Joshua-Benfell/ECEN405_ClassDAmplifier/figures/1.1_Waves (3).png

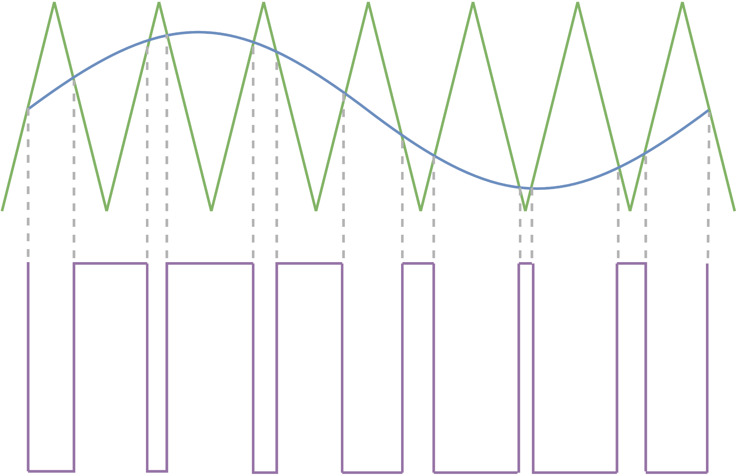
figures/1.1_Waves (3).png
