Joshua-Benfell/ECEN405_ClassDAmplifier/figures/5vSupply.png

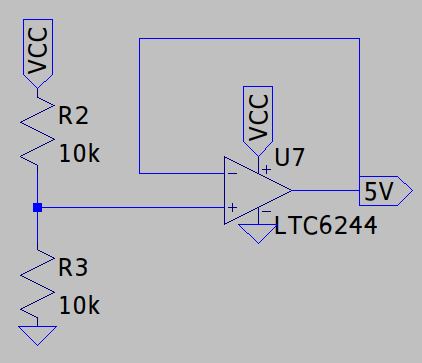
figures/5vSupply.png
