Joshua-Benfell/ECEN405_ClassDAmplifier/figures/angle2.jpg

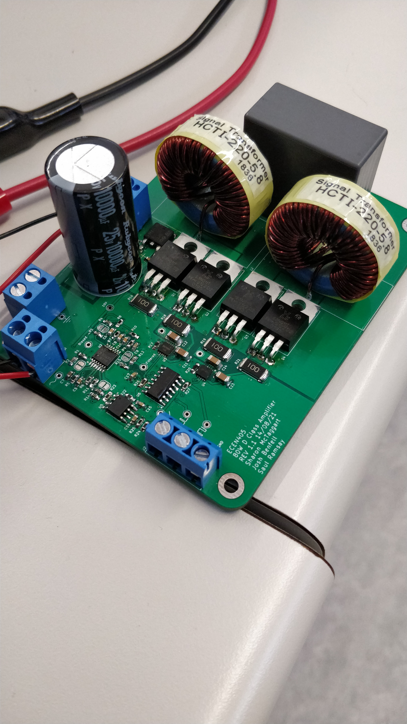
figures/angle2.jpg
