Joshua-Benfell/ECEN405_ClassDAmplifier/figures/backPCB.png

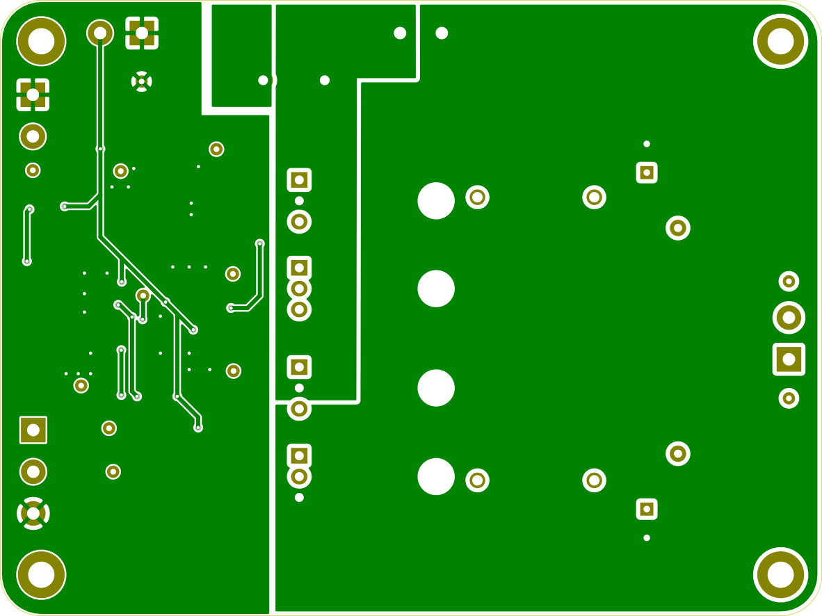
figures/backPCB.png
