Joshua-Benfell/ECEN405_ClassDAmplifier/figures/BiasedSignal.JPG

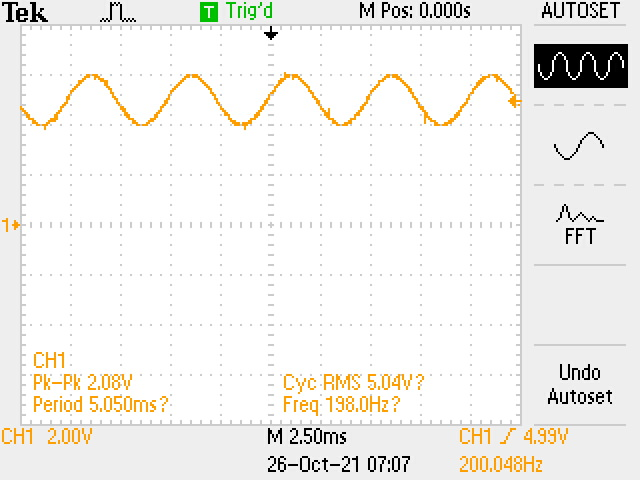
figures/BiasedSignal.JPG
