Joshua-Benfell/ECEN405_ClassDAmplifier/figures/biasingHPF.png

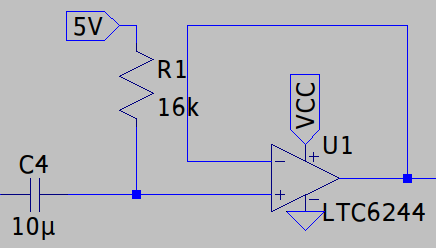
figures/biasingHPF.png
