Joshua-Benfell/ECEN405_ClassDAmplifier/figures/bodeChart.png

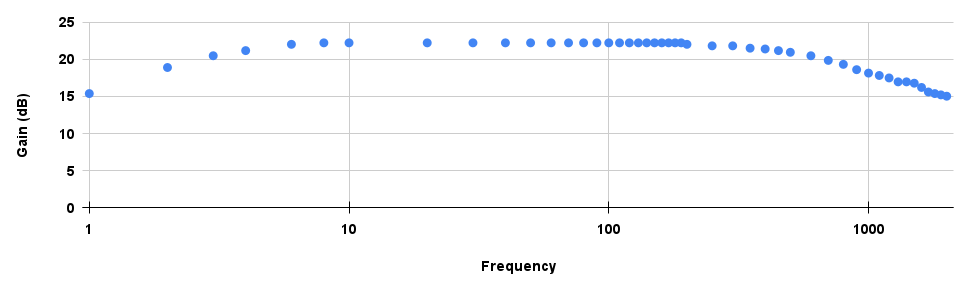
figures/bodeChart.png
