Joshua-Benfell/ECEN405_ClassDAmplifier/figures/bothPWM.JPG

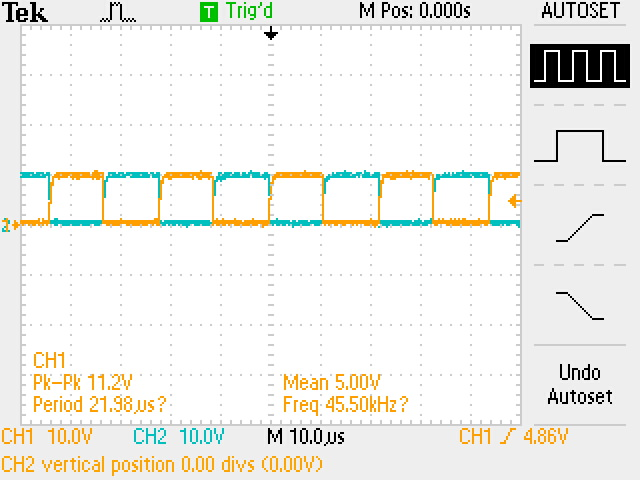
figures/bothPWM.JPG
