Joshua-Benfell/ECEN405_ClassDAmplifier/figures/bpfBode.png

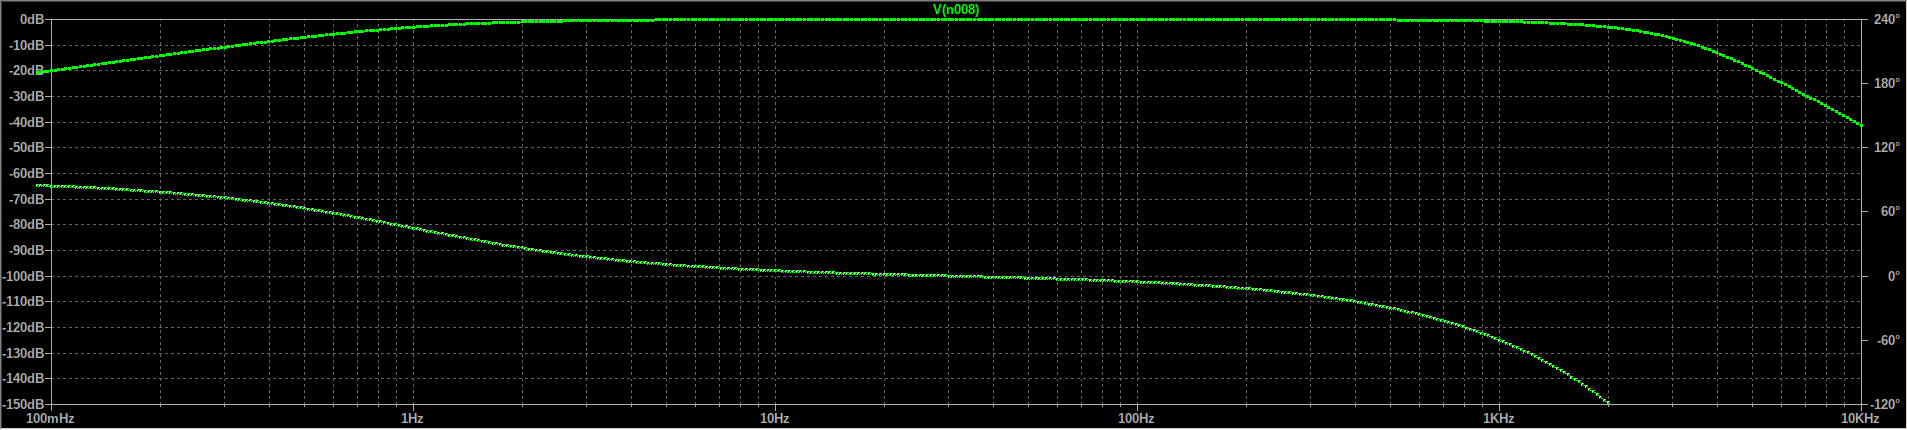
figures/bpfBode.png
