Joshua-Benfell/ECEN405_ClassDAmplifier/figures/Deadtime.png

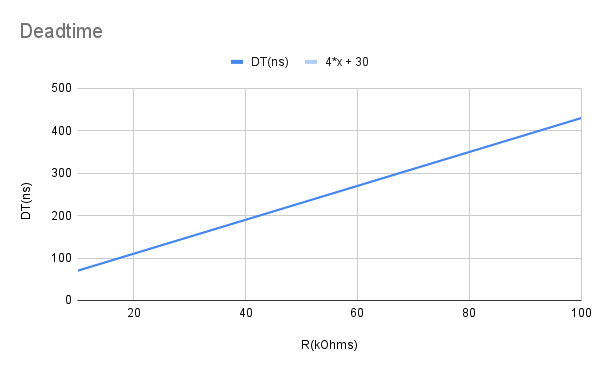
figures/Deadtime.png
