Joshua-Benfell/ECEN405_ClassDAmplifier/figures/efficiencyChart.png

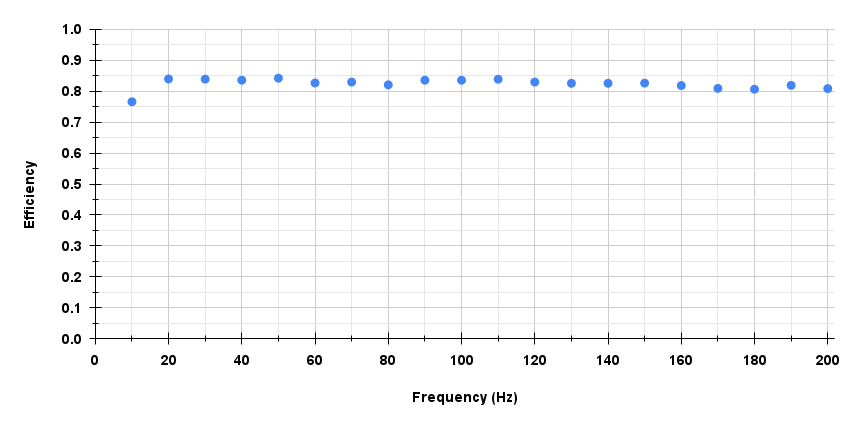
figures/efficiencyChart.png
