Joshua-Benfell/ECEN405_ClassDAmplifier/figures/frontPCB.png

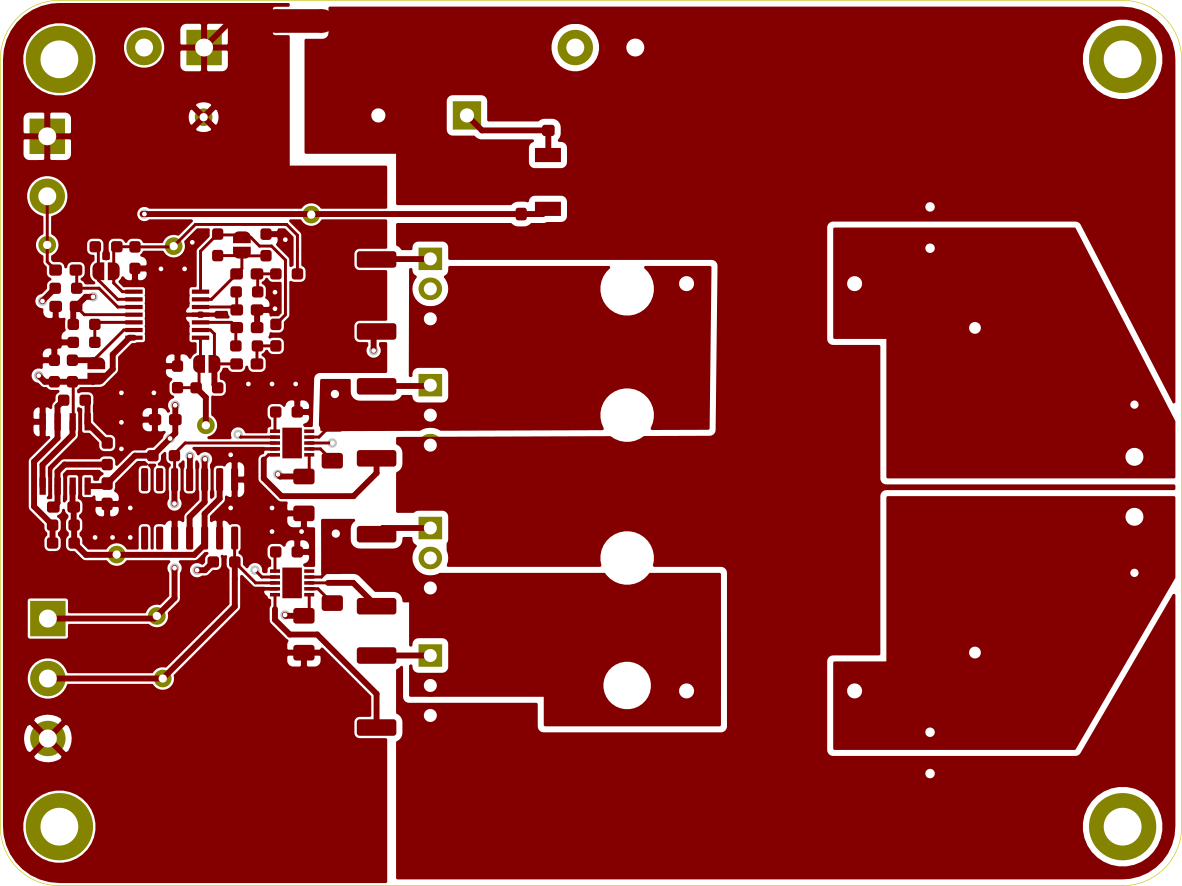
figures/frontPCB.png
