Joshua-Benfell/ECEN405_ClassDAmplifier/figures/fullbridge.jpg

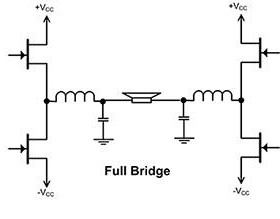
figures/fullbridge.jpg
