Joshua-Benfell/ECEN405_ClassDAmplifier/figures/highDCPWM.JPG

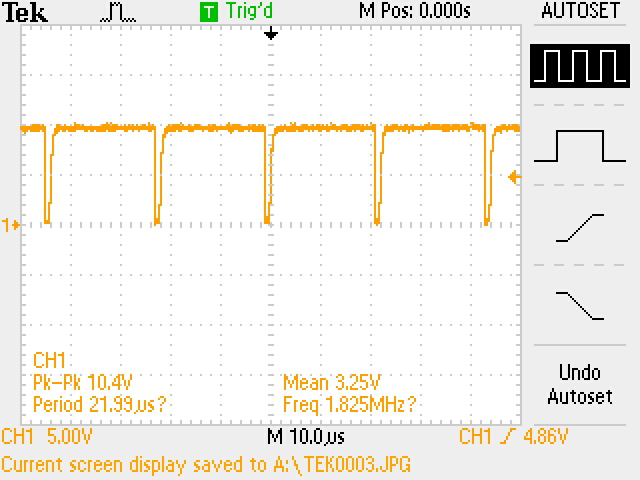
figures/highDCPWM.JPG
