Joshua-Benfell/ECEN405_ClassDAmplifier/figures/hpfBode.png

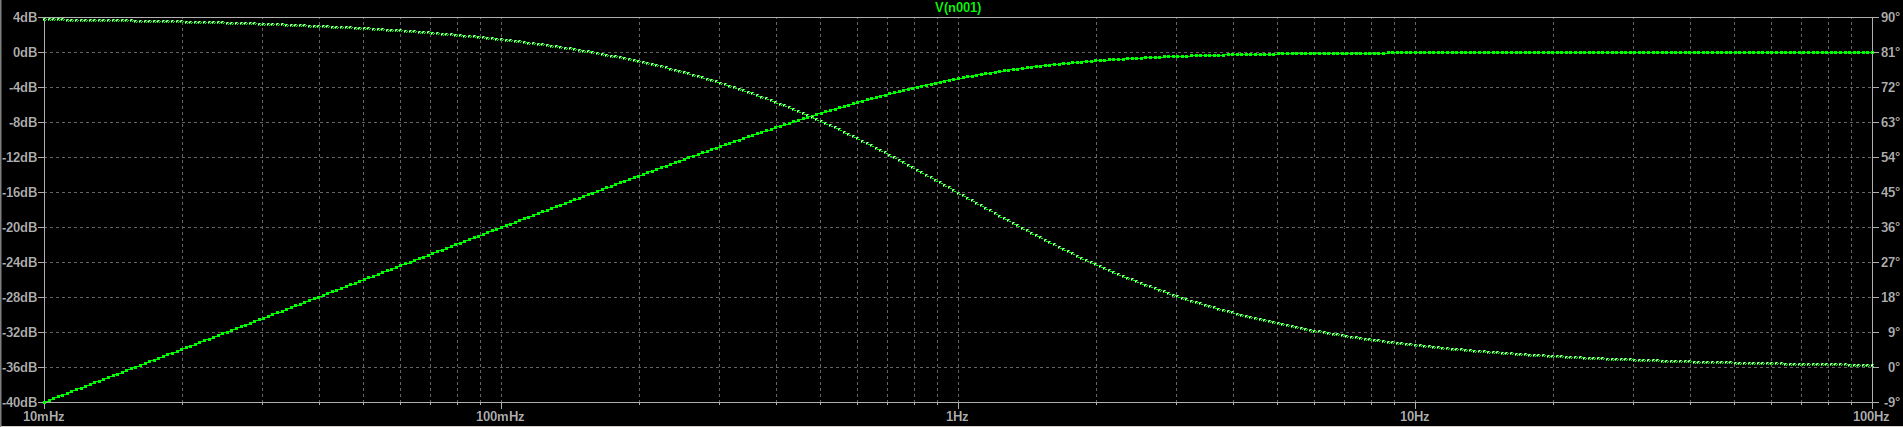
figures/hpfBode.png
