Joshua-Benfell/ECEN405_ClassDAmplifier/figures/outputFilterBode.png

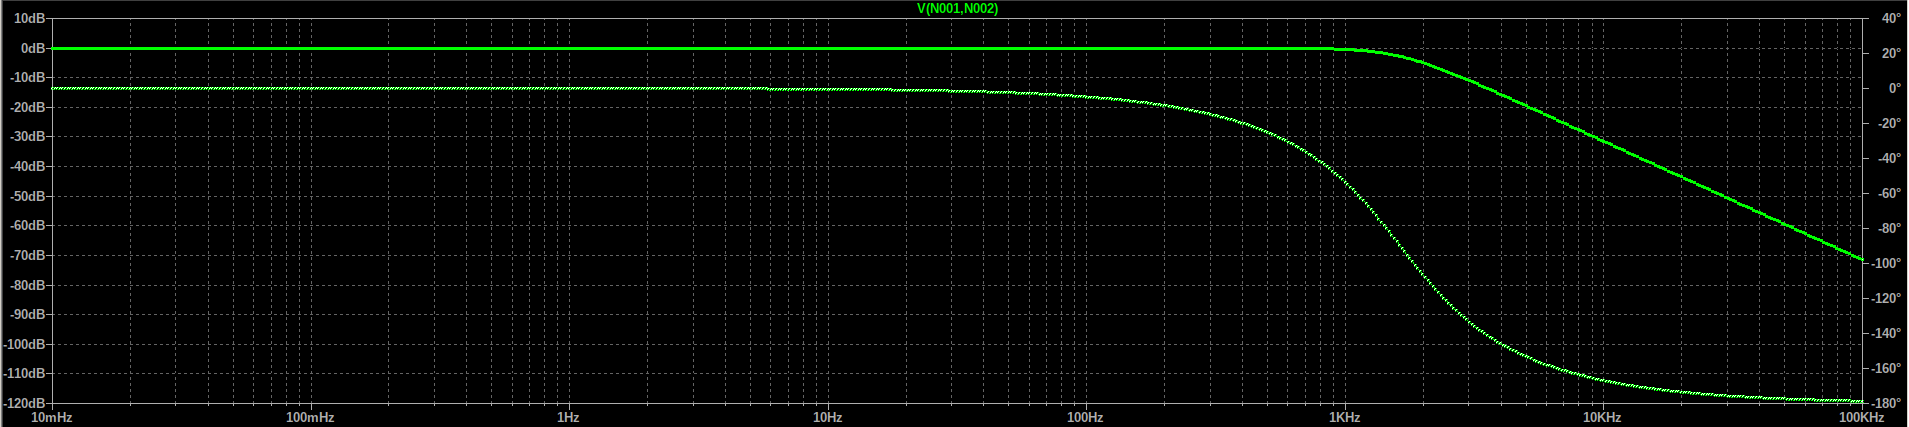
figures/outputFilterBode.png
