Joshua-Benfell/ECEN405_ClassDAmplifier/figures/outputSignalLoadedBySpeaker.JPG

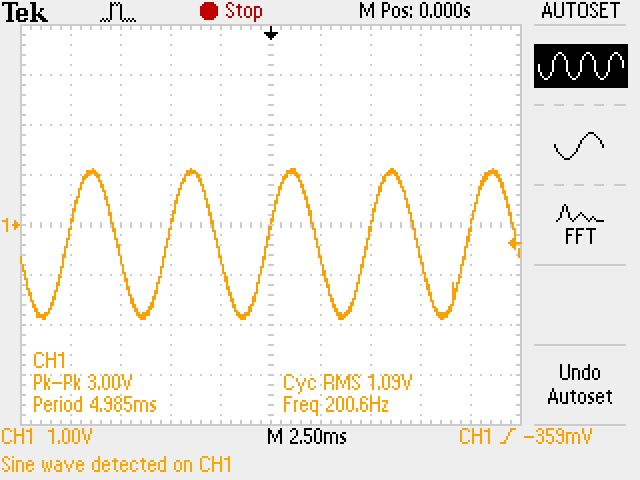
figures/outputSignalLoadedBySpeaker.JPG
