Joshua-Benfell/ECEN405_ClassDAmplifier/figures/systemBlockDiagram.png

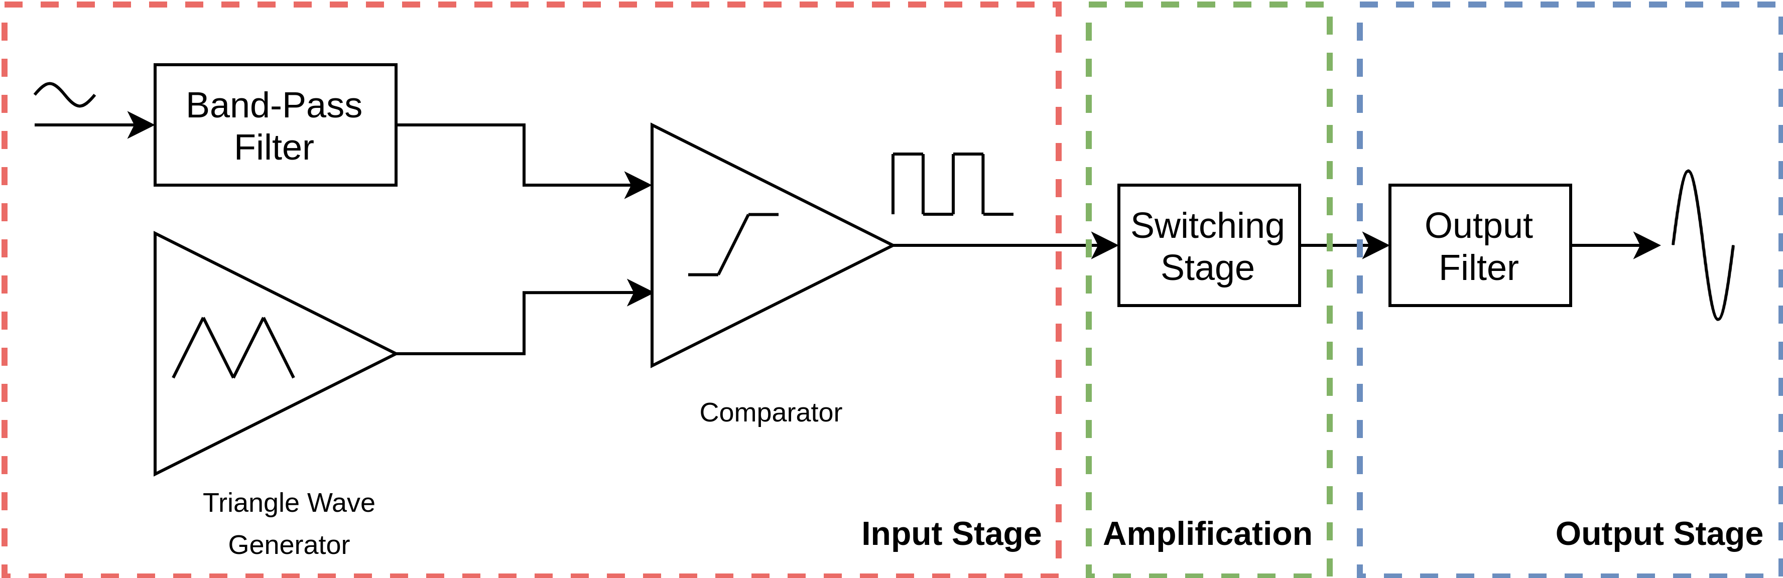
figures/systemBlockDiagram.png
