Joshua-Benfell/ECEN405_ClassDAmplifier/figures/THD.jpg

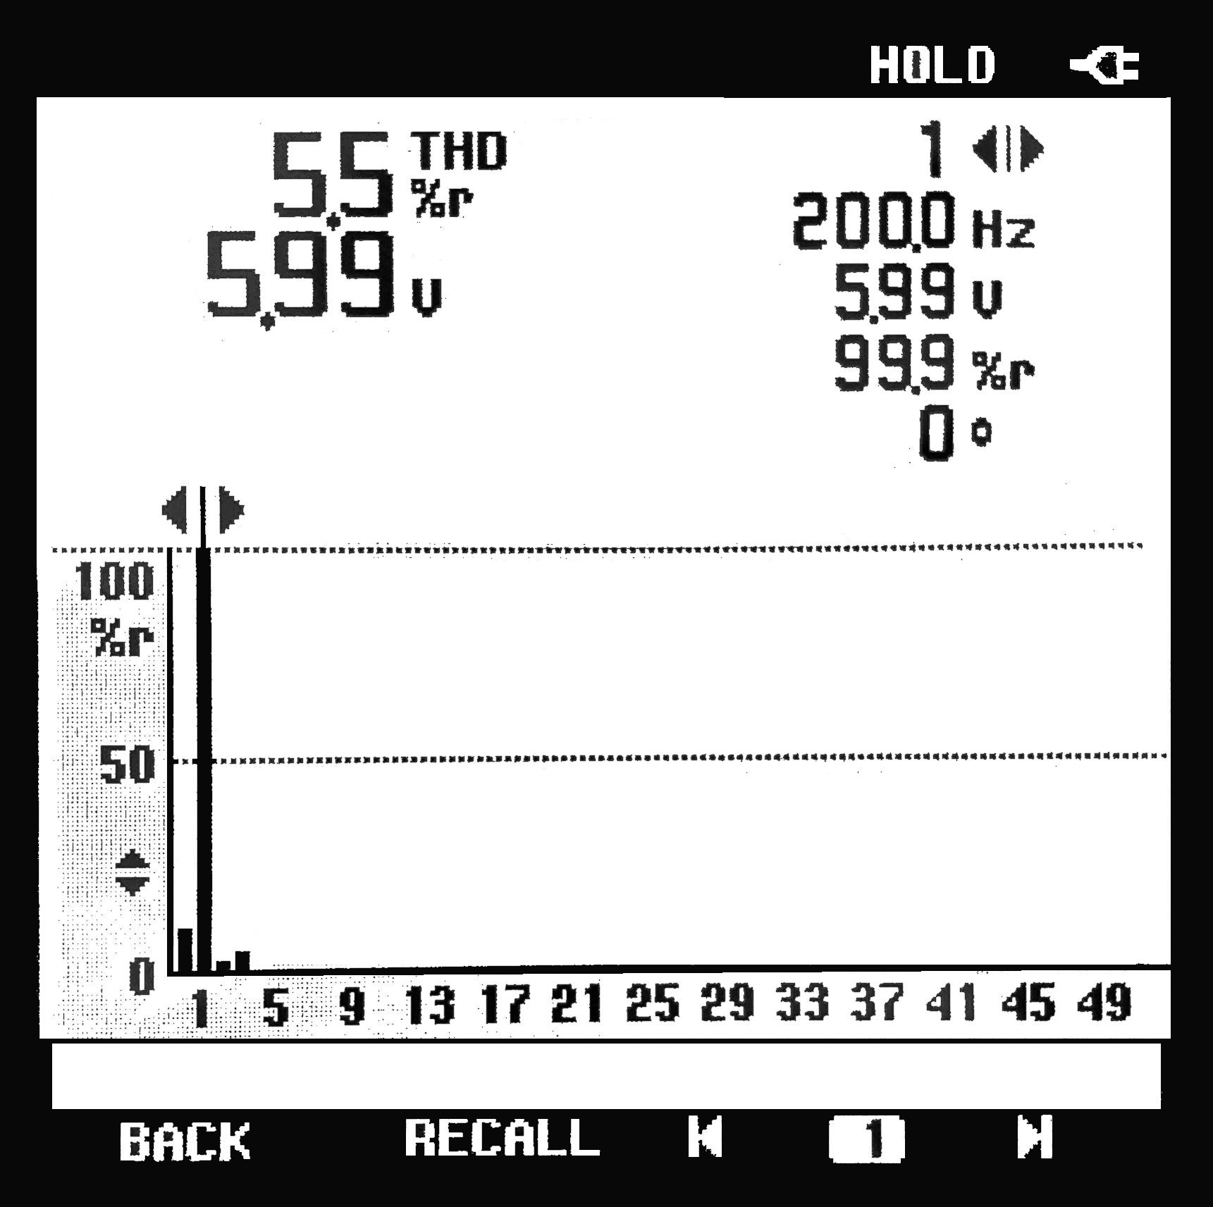
figures/THD.jpg
