Joshua-Benfell/ECEN405_ClassDAmplifier/figures/THDChart.png

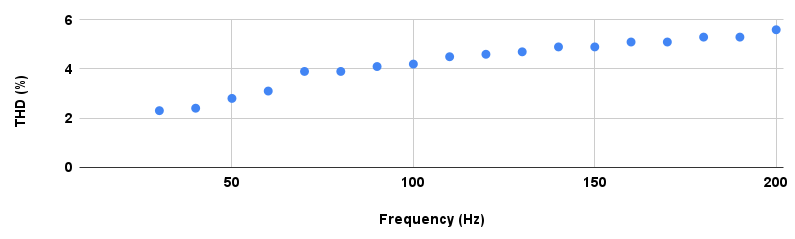
figures/THDChart.png
