Joshua-Benfell/ECEN405_ClassDAmplifier/figures/topdown.jpg

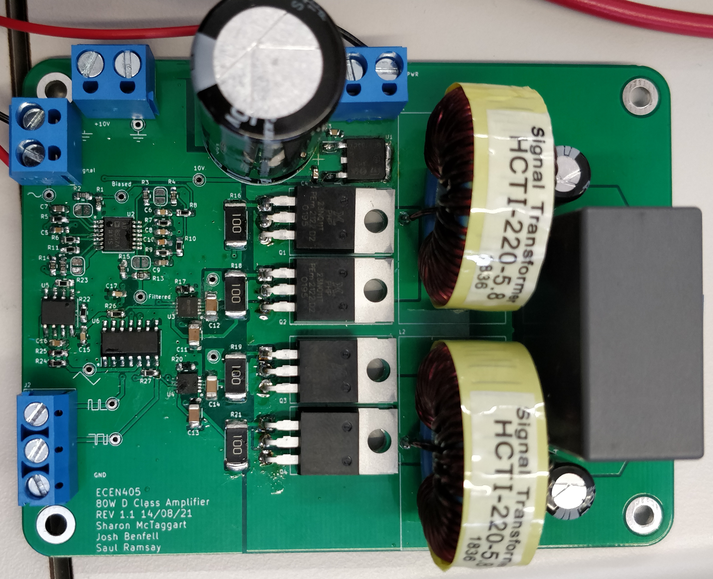
figures/topdown.jpg
