Joshua-Benfell/ECEN405_ClassDAmplifier/figures/triangleOverlappingSignal.JPG

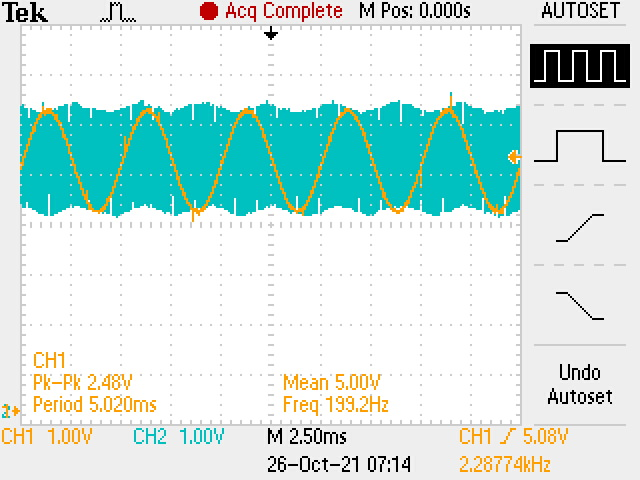
figures/triangleOverlappingSignal.JPG
