Joshua-Benfell/ECEN405_ClassDAmplifier/figures/TriangleWave.JPG

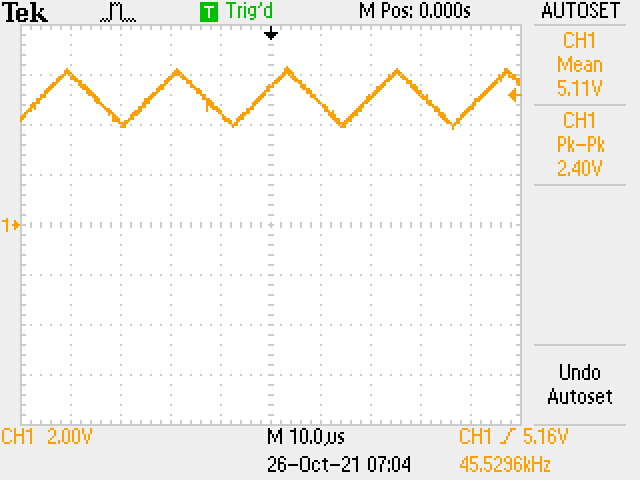
figures/TriangleWave.JPG
