Joshua-Benfell/ECEN405_ClassDAmplifier/figures/triangleWave.png

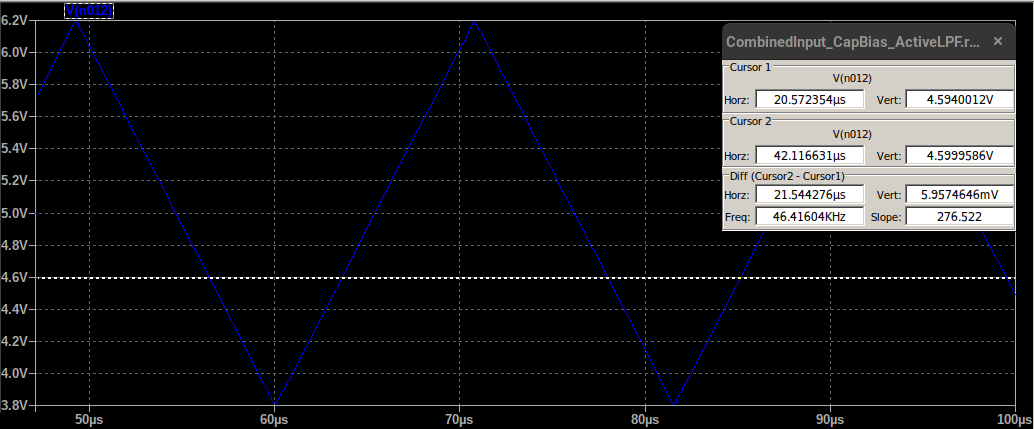
figures/triangleWave.png
