Joshua-Benfell/ECEN405_ClassDAmplifier/figures/triangleWaveGenerator.png

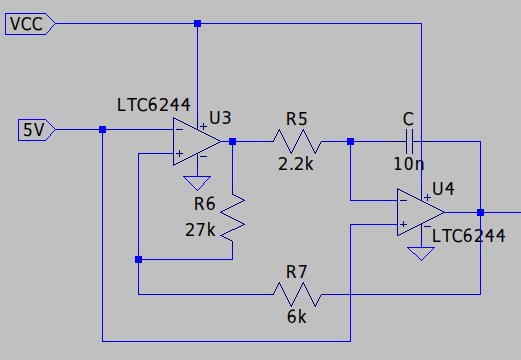
figures/triangleWaveGenerator.png
