Joshua-Benfell/ECEN405_ClassDAmplifier/Kicad/Output/Output1A.png

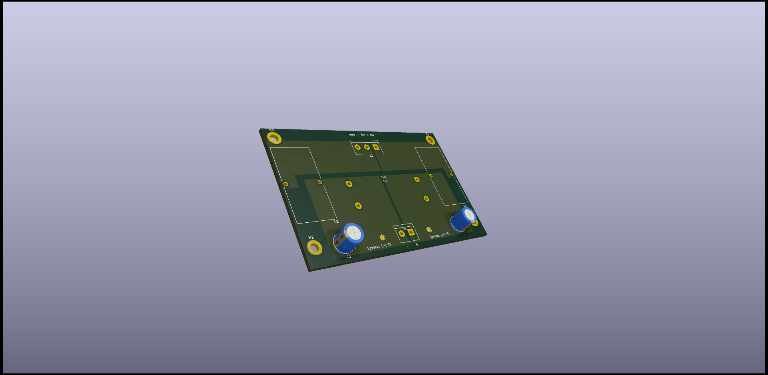
Kicad/Output/Output1A.png
