Joshua-Benfell/ECEN405_ClassDAmplifier/Kicad/Output/Output2.png

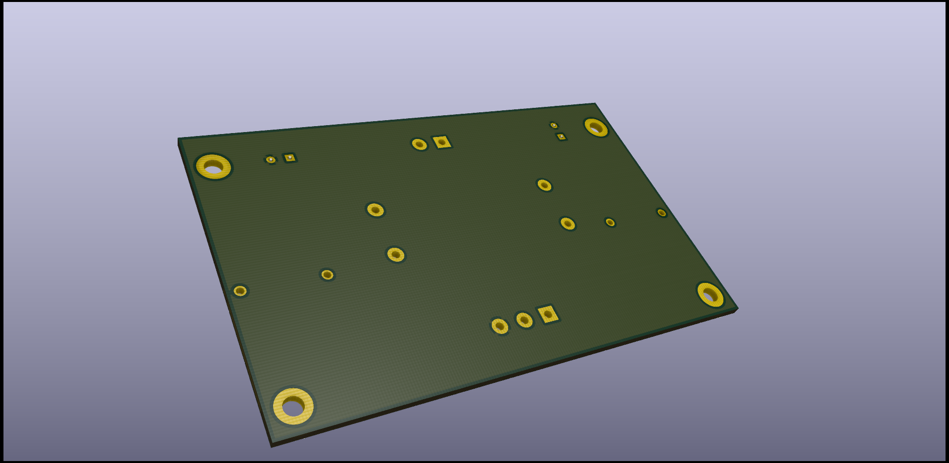
Kicad/Output/Output2.png
