Joshua-Benfell/ECEN405_ClassDAmplifier/figures/secondOrderLPF.png

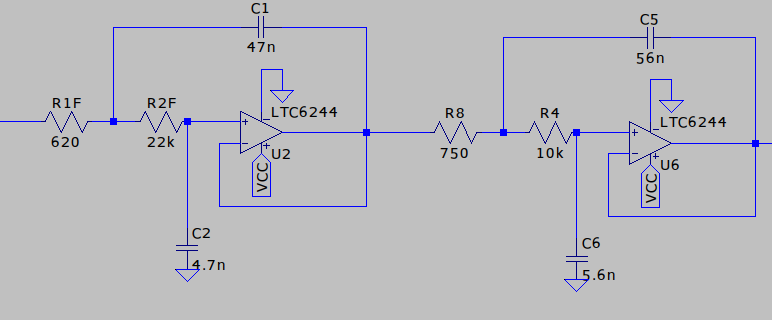
figures/secondOrderLPF.png
