Joshua-Benfell/ECEN405_ClassDAmplifier/spice/FinalDesign.asc

C1: cap; 10n
C2: cap; 10n
C3: cap; 10n
C4: cap; 10µ
C: cap; 10n
R1: res; 16k
R1F: res; 3.9k
R2F: res; 3.9k
R5: res; 2.7k
R6: res; 27k
R7: res; 6k
R8: res; 10k
R9: res; 10k
R10: res; 7.5k
RA: res; 1k
RB: res; 820k
U1: LTC6244
U2: LTC6244
U3: LTC6244
U4: LTC6244
U5: LTC6244
V1: voltage; 10
V2: voltage; SINE(0 1 10)
Named nets: 0, VCC
.tran 0 1s 0 1ms
