Joshua-Benfell/ECEN405_ClassDAmplifier/spice/FinalOutputFilter.asc

C1: cap; {C_BTL}
C2: cap; {C_g}
C3: cap; {C_g}
L1: ind; {L}
L2: ind; {L}
R1: res; 4
V1: voltage; ""; AC 1
Named nets: 0
.param L=270u C_g=3.3u C_BTL=16u
.ac dec 100 10m 1Meg
