Joshua-Benfell/ECEN405_ClassDAmplifier/spice/CombinedInput_CapBias_ActiveLPF.asc

C1: cap; 47n
C2: cap; 4.7n
C3: cap; 10n
C4: cap; 10µ
C5: cap; 56n
C6: cap; 5.6n
C: cap; 10n
R1: res; 16k
R1F: res; 620
R2: res; 10k
R2F: res; 22k
R3: res; 10k
R4: res; 10k
R5: res; 2.2k
R6: res; 27k
R7: res; 6k
R8: res; 750
R10: res; 7.5k
U1: LTC6244
U2: LTC6244
U3: LTC6244
U4: LTC6244
U5: LTC6244
U6: LTC6244
U7: LTC6244
V1: voltage; 10
V2: voltage; SINE(0 1 200); AC 1
Named nets: 0, VCC, 5V
.ac dec 100 10m 1Meg
