Joshua-Benfell/ECEN405_ClassDAmplifier/spice/outputFilter.asc

C1: cap; {C}
C2: cap; {C}
C4: cap; {C}
C5: cap; {C}
L1: ind; {L}
L2: ind; {L}
R1: res; {R}
R2: res; {R}
R3: res; 4
V1: voltage; ""; AC 1
Named nets: 0
.ac dec 100 1 2Meg
.param L=80u C=20u R=1.4
