Joshua-Benfell/ECEN405_ClassDAmplifier/spice/NewCombinedInput_CapacitorBias.asc

C1: cap; 10n
C2: cap; 10n
C3: cap; 10n
C4: cap; 10µ
R1: res; 10k
R2: res; 10k
R3: res; 7.5k
R5: res; 5k
R6: res; 27k
R7: res; 6k
R8: res; 10k
R9: res; 10k
R10: res; 7.5k
U3: LTC6244
U4: LTC6244
U5: LTC6244
V1: voltage; 10
V2: voltage; SINE(0 1 200)
V5: voltage; 10
Named nets: 0, VCC
.tran 0 10ms 0 10ns
