Joshua-Benfell/ECEN405_ClassDAmplifier/spice/CombinedInput.asc

C1: cap; 10n
C2: cap; 10n
C3: cap; 10n
R1: res; 10k
R2: res; 10k
R3: res; 7.5k
R4: res; 7.5k
R5: res; 5k
R6: res; 27k
R7: res; 6k
R8: res; 10k
R9: res; 10k
R10: res; 7.5k
U1: LTC6244
U2: LTC6244
U3: LTC6244
U4: LTC6244
U5: LTC6244
V1: voltage; 10
V2: voltage; 2.5
V3: voltage; SINE(0 1 200); AC 1
V4: voltage; 5
V5: voltage; 10
Named nets: 0, VCC
.tran 0 10m 0 0.01m
