Joshua-Benfell/ECEN405_ClassDAmplifier/spice/Triangle Wave Gen 10V.asc

C1: cap; 10n
C2: cap; 10n
R1: res; 5k
R2: res; 6k
R3: res; 27k
R4: res; 10k
R5: res; 10k
R6: res; 7500
U1: LTC6244
U2: LTC6244
V1: voltage; 10
Vin: voltage; SINE(0 1 200)
Named nets: 0
.tran 0 1s 0 1us
