Joshua-Benfell/ECEN405_ClassDAmplifier/spice/summing opamp.asc

C1: cap; 10n
R1: res; 10k
R2: res; 10k
R3: res; 10k
R4: res; 1k
R5: res; 7500
R6: res; 10k
R7: res; 1k
R8: res; 10k
U1: LTC6244
U2: LTC6244
V1: voltage; SINE(0 1 200)
V2: voltage; 10
V3: voltage; 5
V4: voltage; -10
Named nets: 0, 10v, -10v
.tran 0 10ms 0 1ms
