Joshua-Benfell/ECEN405_ClassDAmplifier/spice/Draft1.asc

R1: res; 10k
R2: res; 10k
R3: res; 10k
R4: res; 10k
U1: LTC6244
U2: LTC6244
V1: voltage; 10
V2: voltage; 2.5
V3: voltage; SINE(0 1 200)
V4: voltage; 5
Named nets: 0, VCC
.tran 0 10m 0 100u
