Joshua-Benfell/ECEN405_ClassDAmplifier/spice/Input.asc

C1: cap; 8n
R1: res; 10k
R2: res; 10k
R3: res; 10k
R4: res; 10k
U1: LTC6244
U2: LTC6244
V1: voltage; 10
V2: voltage; 2.5
V3: voltage; SINE(0 1 200); AC 1
V4: voltage; 5
Named nets: 0, VCC
.ac dec 100 10m 20k
