Joshua-Benfell/ECEN405_ClassDAmplifier/spice/Triangle Wave Gen.asc

C1: cap; 10n
R1: res; 2.4k
R2: res; 12k
R3: res; 27k
R4: res; 10k
R5: res; 4.7k
U1: LTC6244
U2: LTC6244
V1: voltage; 5
Named nets: 0
.tran 0 1ms 0 10ns
